IR2110/VVVF_ArduinoMicro/VVVF_test1/VVVF_test1.ino

#include <avr/interrupt.h>
#include <avr/io.h>
#include <avr/pgmspace.h>

#define LUT_ZERO_LEVEL 127
#define SIN_LENGTH 256

#define F_CPU 16000000UL
#define PRESCALER_VALUE 8
#define TIMER_CLOCK (F_CPU / PRESCALER_VALUE)

//注意: これでモータを実際に駆動しないように！

const uint8_t SIN_U[SIN_LENGTH] PROGMEM = { 127, 130, 133, 136, 139, 142, 145, 148, 151, 154, 157, 160, 163, 166, 169, 172, 175, 178, 181, 184, 186, 189, 192, 194, 197, 200, 202, 205, 207,
                                            209, 212, 214, 216, 218, 221, 223, 225, 227, 229, 230, 232, 234, 235, 237, 239, 240, 241, 243, 244, 245, 246, 247, 248, 249, 250, 250, 251, 252,
                                            252, 253, 253, 253, 253, 253, 254, 253, 253, 253, 253, 253, 252, 252, 251, 250, 250, 249, 248, 247, 246, 245, 244, 243, 241, 240, 239, 237, 235,
                                            234, 232, 230, 229, 227, 225, 223, 221, 218, 216, 214, 212, 209, 207, 205, 202, 200, 197, 194, 192, 189, 186, 184, 181, 178, 175, 172, 169, 166,
                                            163, 160, 157, 154, 151, 148, 145, 142, 139, 136, 133, 130, 127, 123, 120, 117, 114, 111, 108, 105, 102, 99, 96, 93, 90, 87, 84, 81, 78,
                                            75, 72, 69, 67, 64, 61, 59, 56, 53, 51, 48, 46, 44, 41, 39, 37, 35, 32, 30, 28, 26, 24, 23, 21, 19, 18, 16, 14, 13,
                                            12, 10, 9, 8, 7, 6, 5, 4, 3, 3, 2, 1, 1, 0, 0, 0, 0, 0, 0, 0, 0, 0, 0, 0, 1, 1, 2, 3, 3,
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

  // 割り込み許可
  TIMSK1 = (1 << ICIE1) | (1 << TOIE1);
  sei();  //割り込み有効化
}

void loop() {
  freq = min(freq + 0.004, 100);
  modulation_index = freq / 70;
  sigwave_index_increment = (uint16_t)(freq / 2 / carrier_freq * SIN_LENGTH);
  delay(1);  //ひとまずテスト用なので厳密性は問わない
}

void update_duties_and_set_ocr() {
  sigwave_index = (sigwave_index + sigwave_index_increment) & (SIN_LENGTH - 1);

  //デューティー計算
  float duty_u = (((float)(pgm_read_byte_near(&SIN_U[sigwave_index]) - LUT_ZERO_LEVEL) * modulation_index / 127 + 0.5f));
  float duty_v = (((float)(pgm_read_byte_near(&SIN_V[sigwave_index]) - LUT_ZERO_LEVEL) * modulation_index / 127 + 0.5f));
  float duty_w = (((float)(pgm_read_byte_near(&SIN_W[sigwave_index]) - LUT_ZERO_LEVEL) * modulation_index / 127 + 0.5f));

  // 過変調してもタイマがぶっこわれないように制限
  duty_u = max(min(duty_u, 1), 0);
  duty_v = max(min(duty_v, 1), 0);
  duty_w = max(min(duty_w, 1), 0);

  // 出力コンペアレジスタに設定
  OCR1A = (uint16_t)(duty_u * top);
  OCR1B = (uint16_t)(duty_v * top);
  OCR1C = (uint16_t)(duty_w * top);
  // TOP値を設定
  ICR1 = top;
}

// カウンタがBOTTOM（谷）に達したとき
ISR(TIMER1_OVF_vect) {
  update_duties_and_set_ocr();
  TCCR1A = 0b10101010;  // 次の更新はTOP（山）
}

// カウンタがTOP（山）に達したとき
ISR(TIMER1_CAPT_vect) {
  update_duties_and_set_ocr();
  TCCR1A = 0b10101000;  // 次の更新はBOTTOM（谷）
}
