IR2110/VVVF_ArduinoMicro/VVVF_test2/LUT.h

#ifndef LUT_H
#define LUT_H

#include <stdint.h>

// 0が正弦波PWM, 1がTHI(1/6), 2がSVM （lut.pyで生成）
#define LUT_ZERO_LEVEL 127
#define SIN_LENGTH 256
const uint8_t SIN_U[3][SIN_LENGTH] PROGMEM = {
    {127, 130, 133, 136, 139, 142, 145, 148, 151, 154, 157, 160, 163, 166, 169, 172, 175, 178, 181, 184, 186, 189, 192, 194, 197, 200, 202, 205, 207,
     209, 212, 214, 216, 218, 221, 223, 225, 227, 229, 230, 232, 234, 235, 237, 239, 240, 241, 243, 244, 245, 246, 247, 248, 249, 250, 250, 251, 252,
     252, 253, 253, 253, 253, 253, 254, 253, 253, 253, 253, 253, 252, 252, 251, 250, 250, 249, 248, 247, 246, 245, 244, 243, 241, 240, 239, 237, 235,
     234, 232, 230, 229, 227, 225, 223, 221, 218, 216, 214, 212, 209, 207, 205, 202, 200, 197, 194, 192, 189, 186, 184, 181, 178, 175, 172, 169, 166,
     163, 160, 157, 154, 151, 148, 145, 142, 139, 136, 133, 130, 127, 123, 120, 117, 114, 111, 108, 105, 102, 99,  96,  93,  90,  87,  84,  81,  78,
     75,  72,  69,  67,  64,  61,  59,  56,  53,  51,  48,  46,  44,  41,  39,  37,  35,  32,  30,  28,  26,  24,  23,  21,  19,  18,  16,  14,  13,
     12,  10,  9,   8,   7,   6,   5,   4,   3,   3,   2,   1,   1,   0,   0,   0,   0,   0,   0,   0,   0,   0,   0,   0,   1,   1,   2,   3,   3,
     4,   5,   6,   7,   8,   9,   10,  12,  13,  14,  16,  18,  19,  21,  23,  24,  26,  28,  30,  32,  35,  37,  39,  41,  44,  46,  48,  51,  53,
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
                                          81,  84,  86,  88,  90,  92,  94,  96,  98,  101, 103, 105, 107, 110, 112, 114, 117, 120, 122,
                                          125, 128, 131, 134, 138, 142, 145, 150, 154, 160, 166, 172, 180, 190, 203, 222, 255};

#endif  // LUT_H
